Plum3489/TRNG/TRNG/Schematic/QRNG.kicad_sch

## KiCad design TRNG/Schematic/QRNG.kicad_sch (2026-06-30)

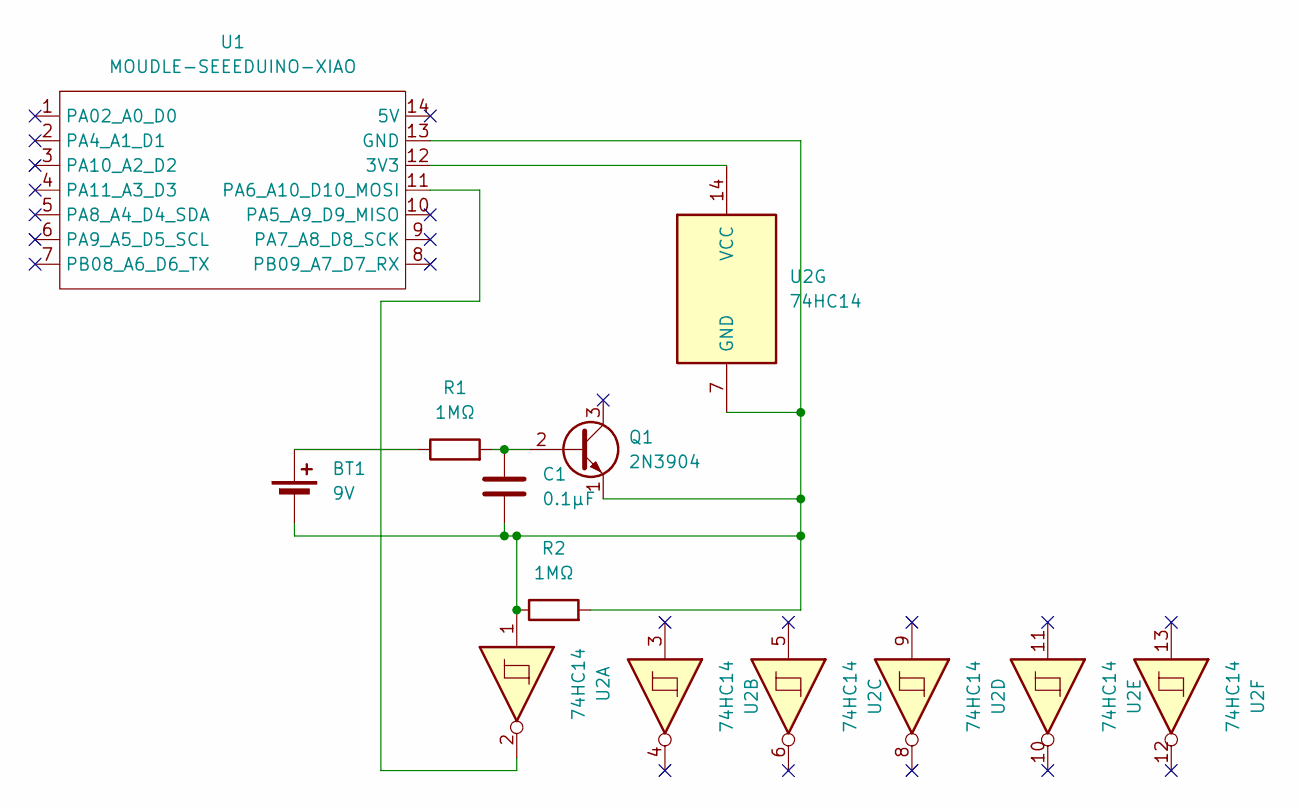
[picture p4: schematic QRNG.kicad_sch]

Parts:
BT1: 9V
C1: 0.1μF
Q1: 2N3904; TO-92_Inline
R1, R2: 1MΩ
U1: MOUDLE-SEEEDUINO-XIAO
U2: 74HC14

Connections:
unnamed: BT1.1 (+), R1.1
unnamed: BT1.2 (-), C1.2, Q1.1 (E), R2.1, R2.2, U1.13 (GND), U2.1, U2.7 (GND)
unnamed: C1.1, Q1.2 (B), R1.2
unnamed: U1.11 (PA6_A10_D10_MOSI), U2.2
unnamed: U1.12 (3V3), U2.14 (VCC)
